eamondoherty618-prog/tracker-firmware/src/can_obd2.cpp

#include "can_obd2.h"

#include <Arduino.h>
#include "driver/twai.h"
#include "tracker_config.h"

// ISO 15765-4 CAN for OBD2: 11-bit functional request 0x7DF answered from
// 0x7E8-0x7EF, with a 29-bit fallback (0x18DB33F1 → 0x18DAF1xx) for vehicles
// that use extended addressing. Single-frame for live PIDs; ISO-TP multi-frame
// (first frame → flow control → consecutive frames) for VIN and long DTC lists.

namespace {

enum class BusState : uint8_t {
  UNINSTALLED,   // driver not installed (boot, or torn down after failed probe)
  LISTENING,     // passive (LISTEN_ONLY): confirm healthy 500k traffic first
  PROBING,       // sending detection requests, waiting for any ECU to answer
  READY,         // bus confirmed — normal polling
  ABSENT,        // probe failed — dormant until the next re-probe window
};

enum class Op : uint8_t { NONE, PROBE, PID, DTC_STORED, DTC_PENDING, VIN, CLEAR };

BusState g_state = BusState::UNINSTALLED;
bool g_extended = false;          // 29-bit addressing in use
uint8_t g_probeAttempts = 0;
uint32_t g_nextProbeMs = 0;       // when ABSENT: earliest re-probe
uint32_t g_lastPollMs = 0;
uint32_t g_lastDtcPollMs = 0;

// In-flight request
Op g_op = Op::NONE;
uint8_t g_opPid = 0;
uint32_t g_opDeadlineMs = 0;
uint8_t g_pidIndex = 0;           // which configured PID the poll cycle is on

// Live values (NAN/negative = never read); *_ms = when last updated
const uint8_t kPids[] = TRACKER_OBD_PIDS;
constexpr size_t kPidCount = sizeof(kPids) / sizeof(kPids[0]);
float g_pidValue[kPidCount];
uint32_t g_pidMs[kPidCount];

// DTCs (decoded "P0301" style), VIN, clear handshake
constexpr size_t MAX_DTC = 8;
String g_dtc[MAX_DTC];      size_t g_dtcCount = 0;
String g_dtcPending[MAX_DTC]; size_t g_dtcPendingCount = 0;
bool g_dtcEverRead = false;
// New-code detection for the instant-post path: a stored-DTC set that changed
// vs the previous read this boot shouldn't wait out the telemetry cadence.
String g_dtcSig; bool g_dtcSigValid = false;
bool g_newDtcEvent = false;
// DTC collection windows: responses from every ECU merge into staging until
// the op deadline, then swap into the live lists in one deterministic step.
String g_dtcStage[MAX_DTC];     size_t g_dtcStageCount = 0;     bool g_dtcWindowGot = false;
String g_dtcPendStage[MAX_DTC]; size_t g_dtcPendStageCount = 0; bool g_dtcPendWindowGot = false;
uint32_t g_lastRxMs = 0;        // last frame heard in READY — silence demotes
uint8_t g_vinTries = 0;         // VIN retry budget per boot
bool g_surveySkipOnce = false;  // heartbeat builder: drop survey when body > budget
// Cold-start crank-voltage capture
bool g_wasRunning = false;
bool g_crankCapture = false;
uint32_t g_crankCaptureEndMs = 0;
float g_crankVMin = NAN;         // min seen during the active capture window
float g_crankVReport = NAN;      // latched result awaiting one telemetry post
String g_vin;
uint32_t g_vinNextMs = 0;   // next VIN request time; retries until captured
bool g_clearRequested = false;
bool g_clearedFlag = false;       // reported once in the next full payload

// ISO-TP reassembly
struct IsoTp {
  bool active = false;
  uint32_t respId = 0;
  uint16_t expected = 0;
  uint16_t got = 0;
  uint8_t nextSn = 1;
  uint32_t lastMs = 0;
  uint8_t buf[64];
} g_isotp;

uint32_t functionalReqId() { return g_extended ? 0x18DB33F1UL : 0x7DFUL; }

bool isObdResponseId(uint32_t id, bool extd) {
  if (g_extended) return extd && (id & 0x1FFFFF00UL) == 0x18DAF100UL;
  return !extd && id >= 0x7E8 && id <= 0x7EF;
}

// Flow-control frame goes to the specific ECU that sent the first frame.
uint32_t flowControlId(uint32_t respId) {
  if (g_extended) {
    const uint8_t ecu = respId & 0xFF;             // 0x18DAF1<ecu>
    return 0x18DA0000UL | ((uint32_t)ecu << 8) | 0xF1UL;  // 0x18DA<ecu>F1
  }
  return respId - 8;                               // 0x7E8 → 0x7E0
}

bool sendFrame(uint32_t id, const uint8_t* data, uint8_t len) {
  twai_message_t msg = {};
  msg.identifier = id;
  msg.extd = g_extended ? 1 : 0;
  // Single-shot: NO hardware retransmission. On a sleeping bus an un-ACKed
  // frame parks the controller at error-passive (bus-off is unreachable) and
  // the TWAI peripheral retransmits it forever — jamming the vehicle's OBD
  // bus all night. Request/response already has op-level timeouts; a lost
  // request is simply retried by the next poll.
  msg.ss = 1;
  msg.data_length_code = 8;                        // ISO 15765-4: pad to 8
  memset(msg.data, 0x00, 8);
  memcpy(msg.data, data, len);
  const bool ok = twai_transmit(&msg, pdMS_TO_TICKS(20)) == ESP_OK;
#if TRACKER_BENCH_DEBUG
  Serial.printf("CAN TX %08lx:", (unsigned long)id);
  for (int i = 0; i < 8; i++) Serial.printf(" %02x", msg.data[i]);
  Serial.println(ok ? "" : "  (tx failed)");
#endif
  return ok;
}

bool sendRequest(const uint8_t* payload, uint8_t len) {
  uint8_t f[8] = { len };
  memcpy(f + 1, payload, len);
  return sendFrame(functionalReqId(), f, len + 1);
}

void beginOp(Op op, uint8_t pid, uint32_t timeoutMs) {
  g_op = op;
  g_opPid = pid;
  g_opDeadlineMs = millis() + timeoutMs;
  g_isotp.active = false;
}

bool startRequestForOp(Op op, uint8_t pid) {
  switch (op) {
    case Op::PROBE:
    case Op::PID: {
      const uint8_t r[] = { 0x01, pid };
      return sendRequest(r, 2);
    }
    case Op::DTC_STORED: { const uint8_t r[] = { 0x03 }; return sendRequest(r, 1); }
    case Op::DTC_PENDING: { const uint8_t r[] = { 0x07 }; return sendRequest(r, 1); }
    case Op::VIN: { const uint8_t r[] = { 0x09, 0x02 }; return sendRequest(r, 2); }
    case Op::CLEAR: { const uint8_t r[] = { 0x04 }; return sendRequest(r, 1); }
    default: return false;
  }
}

// Decode one DTC byte pair to the standard P/C/B/U code string.
String decodeDtc(uint8_t a, uint8_t b) {
  static const char kSys[4] = { 'P', 'C', 'B', 'U' };
  char code[6];
  snprintf(code, sizeof(code), "%c%01X%01X%01X%01X",
           kSys[(a >> 6) & 0x3], (a >> 4) & 0x3, a & 0xF, (b >> 4) & 0xF, b & 0xF);
  return String(code);
}

void parseDtcPayload(const uint8_t* d, uint16_t len, String* out, size_t* outCount) {
  // d[0] = 0x43/0x47, d[1] = count, then 2-byte pairs.
  *outCount = 0;
  if (len < 2) return;
  const uint8_t n = d[1];
  for (uint8_t i = 0; i < n && *outCount < MAX_DTC; i++) {
    const uint16_t off = 2 + i * 2;
    if (off + 1 >= len) break;
    if (d[off] == 0 && d[off + 1] == 0) continue;  // padding pair
    out[(*outCount)++] = decodeDtc(d[off], d[off + 1]);
  }
}

void handlePidValue(uint8_t pid, const uint8_t* ab, uint16_t len) {
  // Key-off placeholder filter: as the bus winds down the ECU answers with
  // 0xFF-filled data ("no value") for a moment. Decoded blindly that's
  // 255 km/h and 100% throttle frozen on the app's vitals card. All-FF is
  // never a legitimate reading for the PIDs we poll — drop the response.
  bool allFF = len > 0;
  for (uint16_t i = 0; i < len; i++) {
    if (ab[i] != 0xFF) { allFF = false; break; }
  }
  if (allFF) return;

  float v = NAN;
  switch (pid) {
    case 0x0C: if (len >= 2) v = ((ab[0] << 8) | ab[1]) / 4.0f; break;  // RPM
    case 0x0D: if (len >= 1) v = ab[0]; break;                          // km/h
    case 0x05: if (len >= 1) v = (float)ab[0] - 40.0f; break;           // coolant °C
    case 0x11: if (len >= 1) v = ab[0] * 100.0f / 255.0f; break;        // throttle %
    case 0x42: if (len >= 2) v = ((ab[0] << 8) | ab[1]) / 1000.0f; break; // control module voltage
    case 0x2F: if (len >= 1) v = ab[0] * 100.0f / 255.0f; break;        // fuel level %
    case 0x10: if (len >= 2) v = ((ab[0] << 8) | ab[1]) / 100.0f; break; // MAF grams/sec
    default:   if (len >= 1) v = ab[0]; break;   // raw first byte for extra PIDs
  }
  for (size_t i = 0; i < kPidCount; i++) {
    if (kPids[i] == pid && !isnan(v)) { g_pidValue[i] = v; g_pidMs[i] = millis(); }
  }

  // Cold-start forensics: capture the LOWEST control-module voltage (PID 0x42)
  // during the engine-start window — the crank/alternator-ramp sag. Trended
  // server-side over weeks, a deepening sag calls a dying battery BEFORE it
  // strands the truck. (True hardware note: this is the sag the tracker can
  // see once it's polling — the deepest starter-motor dip may pre-date the
  // first poll, but the trend of what we DO catch is what matters.)
  if (pid == 0x42 && g_crankCapture && !isnan(v) && v > 6.0f) {
    if (isnan(g_crankVMin) || v < g_crankVMin) g_crankVMin = v;
  }
}

// A fully reassembled (or single-frame) OBD payload for the in-flight op.
// Union one responder's codes into a staging set (dedup, capped). DTC ops
// collect from ALL ECUs until the op deadline — first-responder-wins made the
// visible set oscillate ECM/TCM and spam instant posts.
void mergeDtcPayload(const uint8_t* d, uint16_t len, String* out, size_t* outCount) {
  String tmp[MAX_DTC]; size_t n = 0;
  parseDtcPayload(d, len, tmp, &n);
  for (size_t i = 0; i < n && *outCount < MAX_DTC; i++) {
    bool dup = false;
    for (size_t j = 0; j < *outCount; j++) if (out[j] == tmp[i]) { dup = true; break; }
    if (!dup) out[(*outCount)++] = tmp[i];
  }
}

void handleObdPayload(const uint8_t* d, uint16_t len) {
  if (len < 1) return;
  const uint8_t svc = d[0];
  // Cross-ECU discipline: a broadcast (0x7DF) request is answered by EVERY
  // emissions ECU. Only a payload that MATCHES the in-flight op may consume
  // it — a TCM's 0x7F negative response must not cancel the ECM's multi-frame
  // VIN mid-reassembly (field bug: the truck's VIN could NEVER be captured
  // because unconditional g_op=NONE ran on the first stray reply). Unmatched
  // payloads are ignored; the op deadline handles true timeouts.
  bool done = false;
  switch (g_op) {
    case Op::PROBE:
      if (svc == 0x41) {
        g_state = BusState::READY;
        g_lastRxMs = millis();
        g_probeAttempts = 0;
        Serial.print("OBD2: bus detected (");
        Serial.print(g_extended ? "29" : "11");
        Serial.println("-bit)");
        if (len >= 4) handlePidValue(d[1], d + 2, len - 2);
        done = true;
      }
      break;
    case Op::PID:
      if (svc == 0x41 && len >= 3 && d[1] == g_opPid) { handlePidValue(d[1], d + 2, len - 2); done = true; }
      break;
    case Op::DTC_STORED:
      // Collect-until-deadline: merge into staging; finalize in canObd2Service.
      if (svc == 0x43) { mergeDtcPayload(d, len, g_dtcStage, &g_dtcStageCount); g_dtcWindowGot = true; }
      break;
    case Op::DTC_PENDING:
      if (svc == 0x47) { mergeDtcPayload(d, len, g_dtcPendStage, &g_dtcPendStageCount); g_dtcPendWindowGot = true; }
      break;
    case Op::VIN:
      // [0x49, 0x02, 0x01, 17 VIN chars]
      if (svc == 0x49 && len >= 4) {
        String vin;
        for (uint16_t i = 3; i < len && vin.length() < 17; i++) {
          const char c = (char)d[i];
          if (c >= '0' && c <= 'Z') vin += c;
        }
        if (vin.length() == 17) { g_vin = vin; Serial.print("OBD2: VIN "); Serial.println(g_vin); done = true; }
      }
      break;
    case Op::CLEAR:
      if (svc == 0x44) {
        g_dtcCount = 0;
        g_dtcPendingCount = 0;
        g_dtcSig = "";
        g_clearedFlag = true;
        Serial.println("OBD2: stored DTCs cleared (server-commanded)");
        done = true;
      }
      break;
    default: break;
  }
  if (done) g_op = Op::NONE;
}

void handleFrame(const twai_message_t& msg) {
#if TRACKER_BENCH_DEBUG
  Serial.printf("CAN RX %08lx:", (unsigned long)msg.identifier);
  for (int i = 0; i < msg.data_length_code; i++) Serial.printf(" %02x", msg.data[i]);
  Serial.println();
#endif
  if (!isObdResponseId(msg.identifier, msg.extd)) return;
  const uint8_t* d = msg.data;
  const uint8_t pci = d[0] >> 4;

  if (pci == 0x0) {                                   // single frame
    const uint8_t len = d[0] & 0xF;
    if (len >= 1 && len <= 7) handleObdPayload(d + 1, len);
  } else if (pci == 0x1) {                            // first frame → flow control
    // First FF wins: a second ECU's multi-frame answer must not clobber an
    // in-progress reassembly (cross-ECU broadcast responses).
    if (g_isotp.active && msg.identifier != g_isotp.respId) return;
    g_isotp.active = true;
    g_isotp.respId = msg.identifier;
    g_isotp.expected = ((d[0] & 0xF) << 8) | d[1];
    if (g_isotp.expected > sizeof(g_isotp.buf)) g_isotp.expected = sizeof(g_isotp.buf);
    g_isotp.got = 0;
    g_isotp.nextSn = 1;
    g_isotp.lastMs = millis();
    for (uint8_t i = 2; i < 8 && g_isotp.got < g_isotp.expected; i++) g_isotp.buf[g_isotp.got++] = d[i];
    const uint8_t fc[] = { 0x30, 0x00, 0x00 };        // continue, no block limit, no delay
    sendFrame(flowControlId(msg.identifier), fc, 3);
  } else if (pci == 0x2 && g_isotp.active && msg.identifier == g_isotp.respId) {  // consecutive
    if ((d[0] & 0xF) != (g_isotp.nextSn & 0xF)) { g_isotp.active = false; return; }
    g_isotp.nextSn++;
    g_isotp.lastMs = millis();
    for (uint8_t i = 1; i < 8 && g_isotp.got < g_isotp.expected; i++) g_isotp.buf[g_isotp.got++] = d[i];
    if (g_isotp.got >= g_isotp.expected) {
      g_isotp.active = false;
      handleObdPayload(g_isotp.buf, g_isotp.got);
    }
  }
}

bool installDriver(bool listenOnly) {
  // LISTEN_ONLY is physically passive: no TX, not even ACK bits. The probe
  // starts there so a mis-wired tap or wrong-bitrate bus can't be disturbed
  // by us — a live vehicle bus carries power steering and worse (field:
  // plugging an unpowered, terminated tap bumped the idle and latched a
  // "service power steering" warning).
  twai_general_config_t g = TWAI_GENERAL_CONFIG_DEFAULT(
      (gpio_num_t)TRACKER_CAN_TX_GPIO, (gpio_num_t)TRACKER_CAN_RX_GPIO,
      listenOnly ? TWAI_MODE_LISTEN_ONLY : TWAI_MODE_NORMAL);
  g.rx_queue_len = 32;
  g.tx_queue_len = 4;
  twai_timing_config_t t = TWAI_TIMING_CONFIG_500KBITS();
  twai_filter_config_t f = TWAI_FILTER_CONFIG_ACCEPT_ALL();
  if (twai_driver_install(&g, &t, &f) != ESP_OK) return false;
  if (twai_start() != ESP_OK) { twai_driver_uninstall(); return false; }
  return true;
}

void teardownDriver() {
  twai_stop();
  twai_driver_uninstall();
}

void goAbsent() {
  teardownDriver();
  g_state = BusState::ABSENT;
  g_nextProbeMs = millis() + TRACKER_OBD_REPROBE_MS;
  g_op = Op::NONE;
  Serial.println("OBD2: no bus detected — dormant (will re-probe when the vehicle is active)");
}

uint32_t g_listenStartMs = 0;
uint32_t g_listenFrames = 0;

// Passive bus survey: an inventory of every CAN ID heard with its latest
// payload bytes. This is the discovery tool for proprietary broadcasts the
// standard OBD2 services can't reach (e.g. GM TPMS tire pressures): deflate a
// tire, watch which ID's byte moves in telemetry. RX-only — gathering it
// never transmits a single frame.
struct SurveyEntry { uint32_t id; uint32_t count; uint8_t len; uint8_t data[8]; };
constexpr size_t MAX_SURVEY = 48;
SurveyEntry g_survey[MAX_SURVEY];
size_t g_surveyCount = 0;

void surveyFrame(const twai_message_t& msg) {
  for (size_t i = 0; i < g_surveyCount; i++) {
    if (g_survey[i].id == msg.identifier) {
      g_survey[i].count++;
      g_survey[i].len = msg.data_length_code;
      memcpy(g_survey[i].data, msg.data, 8);
      return;
    }
  }
  if (g_surveyCount < MAX_SURVEY) {
    SurveyEntry& e = g_survey[g_surveyCount++];
    e.id = msg.identifier;
    e.count = 1;
    e.len = msg.data_length_code;
    memcpy(e.data, msg.data, 8);
  }
}

void startProbe() {
  // Phase 1: passive listen. Healthy 500k traffic (frames received, no bus
  // errors) is required before we ever transmit a bit.
  if (g_state == BusState::UNINSTALLED || g_state == BusState::ABSENT) {
    if (!installDriver(true)) { g_state = BusState::ABSENT; g_nextProbeMs = millis() + TRACKER_OBD_REPROBE_MS; return; }
  }
  g_state = BusState::LISTENING;
  g_listenStartMs = millis();
  g_listenFrames = 0;
  g_probeAttempts = 0;
  g_extended = false;
  g_op = Op::NONE;
}

}  // namespace

void canObd2Init() {
  for (size_t i = 0; i < kPidCount; i++) { g_pidValue[i] = NAN; g_pidMs[i] = 0; }

#if TRACKER_BENCH_DEBUG
  // RX idle check: a powered, healthy transceiver holds RXD HIGH (recessive)
  // when the bus is quiet. LOW/floating here = dead unit logic or a broken
  // white lead — distinguishes them from ESP32-side faults without a meter.
  pinMode(TRACKER_CAN_RX_GPIO, INPUT);
  delay(5);
  Serial.printf("CAN: RX line idle = %s (HIGH = transceiver alive)\n",
                digitalRead(TRACKER_CAN_RX_GPIO) ? "HIGH" : "LOW");
#endif

#if TRACKER_BENCH_DEBUG && !TRACKER_CAN_LISTEN_ONLY_LOCK
  // Line-load test: drive TX as a plain GPIO and read it back. A healthy,
  // unpowered-or-listening transceiver input barely loads the pin; a damaged
  // TXD input clamps it, and the readback disagrees with what we drive.
  {
    pinMode(TRACKER_CAN_TX_GPIO, OUTPUT);
    digitalWrite(TRACKER_CAN_TX_GPIO, HIGH);
    delayMicroseconds(50);
    const int readHigh = digitalRead(TRACKER_CAN_TX_GPIO);
    digitalWrite(TRACKER_CAN_TX_GPIO, LOW);
    delayMicroseconds(50);
    const int readLow = digitalRead(TRACKER_CAN_TX_GPIO);
    digitalWrite(TRACKER_CAN_TX_GPIO, HIGH);  // leave recessive
    Serial.printf("CAN: TX line-load test: drive HIGH reads %s, drive LOW reads %s%s\n",
                  readHigh ? "HIGH" : "LOW", readLow ? "LOW(ok)" : "LOW(ok)",
                  readHigh ? " — line free" : " — LINE CLAMPED (unit TXD input suspect)");
    pinMode(TRACKER_CAN_TX_GPIO, INPUT);
  }

  // Desk self-test: transmit one frame in NO_ACK mode and listen for our own
  // echo through the transceiver. Straight TX/RX wiring = echo received;
  // crossed Grove leads = silence. This resolves the wiring question WITHOUT
  // a vehicle (bench only — this mode transmits, so it is compiled out of
  // bench_listen and must never run plugged into a live bus).
  {
    twai_general_config_t g = TWAI_GENERAL_CONFIG_DEFAULT(
        (gpio_num_t)TRACKER_CAN_TX_GPIO, (gpio_num_t)TRACKER_CAN_RX_GPIO, TWAI_MODE_NO_ACK);
    twai_timing_config_t t = TWAI_TIMING_CONFIG_500KBITS();
    twai_filter_config_t f = TWAI_FILTER_CONFIG_ACCEPT_ALL();
    bool pass = false;
    if (twai_driver_install(&g, &t, &f) == ESP_OK && twai_start() == ESP_OK) {
      twai_message_t tx = {};
      tx.identifier = 0x555;
      tx.self = 1;               // self-reception request: loop back via the bus pins
      tx.data_length_code = 2;
      tx.data[0] = 0xAB; tx.data[1] = 0xCD;
      if (twai_transmit(&tx, pdMS_TO_TICKS(100)) == ESP_OK) {
        twai_message_t rx;
        if (twai_receive(&rx, pdMS_TO_TICKS(300)) == ESP_OK && rx.identifier == 0x555) pass = true;
      }
      // Error autopsy: the counters say WHY an echo died. High bus/tx errors =
      // we transmitted but the bus never reflected it (transceiver mute or
      // dead driver). Clean counters + no echo = frame never made it out.
      twai_status_info_t st;
      if (twai_get_status_info(&st) == ESP_OK) {
        Serial.printf("CAN: post-test state=%d tx_err=%lu rx_err=%lu bus_err=%lu tx_failed=%lu arb_lost=%lu\n",
                      (int)st.state, (unsigned long)st.tx_error_counter, (unsigned long)st.rx_error_counter,
                      (unsigned long)st.bus_error_count, (unsigned long)st.tx_failed_count,
                      (unsigned long)st.arb_lost_count);
      }
      twai_stop();
      twai_driver_uninstall();
    }
    Serial.println(pass
      ? "CAN self-test: PASS — TX/RX wiring to the transceiver is good"
      : "CAN self-test: FAIL — no echo; yellow/white Grove leads likely crossed (or unit unpowered)");

    // Slow-speed retry: marginal/damaged analog paths sometimes pass at
    // 125 kbps while failing at 500. A split verdict is its own fingerprint.
    if (!pass) {
      twai_general_config_t g2 = TWAI_GENERAL_CONFIG_DEFAULT(
          (gpio_num_t)TRACKER_CAN_TX_GPIO, (gpio_num_t)TRACKER_CAN_RX_GPIO, TWAI_MODE_NO_ACK);
      twai_timing_config_t t2 = TWAI_TIMING_CONFIG_125KBITS();
      twai_filter_config_t f2 = TWAI_FILTER_CONFIG_ACCEPT_ALL();
      bool slowPass = false;
      if (twai_driver_install(&g2, &t2, &f2) == ESP_OK && twai_start() == ESP_OK) {
        twai_message_t tx2 = {};
        tx2.identifier = 0x556;
        tx2.self = 1;
        tx2.data_length_code = 1;
        tx2.data[0] = 0x5A;
        if (twai_transmit(&tx2, pdMS_TO_TICKS(100)) == ESP_OK) {
          twai_message_t rx2;
          if (twai_receive(&rx2, pdMS_TO_TICKS(300)) == ESP_OK && rx2.identifier == 0x556) slowPass = true;
        }
        twai_stop();
        twai_driver_uninstall();
      }
      Serial.println(slowPass
        ? "CAN self-test @125k: PASS — analog path marginal at 500k (damaged but limping)"
        : "CAN self-test @125k: FAIL — transmit path hard-dead at any speed");
    }
  }
#endif

  startProbe();
}

void canObd2RequestClearDtc() {
  if (g_state != BusState::READY) { Serial.println("OBD2: clear requested but bus not present"); return; }
  g_clearRequested = true;
}

bool canObd2Present() { return g_state == BusState::READY; }

bool canObd2TakeNewDtcEvent() {
  const bool e = g_newDtcEvent;
  g_newDtcEvent = false;
  return e;
}

bool canObd2EngineRunning() {
  // Fresh RPM (0x0C) reading above the idle floor = engine on.
  for (size_t i = 0; i < kPidCount; i++) {
    if (kPids[i] == 0x0C) {
      return g_pidMs[i] != 0 && (millis() - g_pidMs[i] < 15000UL) && g_pidValue[i] > 250.0f;
    }
  }
  return false;
}

void canObd2Service(bool vehicleActive) {
  const uint32_t now = millis();

  // Drain everything the controller has for us — cheap, no blocking.
  if (g_state == BusState::PROBING || g_state == BusState::READY) {
    twai_message_t msg;
    while (twai_receive(&msg, 0) == ESP_OK) { g_lastRxMs = now; surveyFrame(msg); handleFrame(msg); }

    // A wedged controller (no transceiver → no ACKs → bus-off) reads as absent.
    twai_status_info_t st;
    if (twai_get_status_info(&st) == ESP_OK && st.state == TWAI_STATE_BUS_OFF) {
      goAbsent();
      return;
    }
  }

  // ISO-TP reassembly timeout
  if (g_isotp.active && now - g_isotp.lastMs > 500) g_isotp.active = false;

  switch (g_state) {
    case BusState::ABSENT:
      // Re-probe on a timer regardless of trip state (the listen phase is
      // passive and harmless on a sleeping bus). Field lesson: an unlucky
      // boot window marked the bus absent and, gated on GPS-motion trips,
      // never retried while the truck idled in the driveway for an hour.
      if ((int32_t)(now - g_nextProbeMs) >= 0) startProbe();
      return;
    case BusState::UNINSTALLED:
      return;
    case BusState::LISTENING: {
#if TRACKER_BENCH_DEBUG
      // Silence must be visible: prove the listener is alive even when the
      // bus is dead quiet (parked truck, desk bench, unplugged tap).
      static uint32_t lastListenLogMs = 0;
      if (now - lastListenLogMs >= 10000UL) {
        lastListenLogMs = now;
        Serial.printf("CAN: listening (%s), %lu frames heard\n",
                      TRACKER_CAN_LISTEN_ONLY_LOCK ? "locked passive" : "pre-probe",
                      (unsigned long)g_listenFrames);
      }
#endif
      // Count anything heard; healthy traffic ⇒ safe to speak. Silence for
      // the whole window ⇒ treat as absent (or parked) and stay passive.
      twai_message_t msg;
      while (twai_receive(&msg, 0) == ESP_OK) {
        g_listenFrames++;
        surveyFrame(msg);
#if TRACKER_BENCH_DEBUG
        if (g_listenFrames <= 5) {
          Serial.printf("CAN LISTEN %08lx dlc=%d\n", (unsigned long)msg.identifier, msg.data_length_code);
        }
#endif
      }
      if (TRACKER_CAN_LISTEN_ONLY_LOCK) {
        // Locked passive: report what we hear, never speak. Frame count goes
        // out in telemetry so the first vehicle session is verifiable without
        // a laptop.
        return;
      }
      // Threshold/window tuned on a live 2017 Silverado: the main loop blocks
      // for seconds at a time during boot (modem bring-up), so early drains
      // only catch a queue's worth of frames — 5s was expiring before 20
      // frames ever accumulated even on a roaring bus. 5 real frames is
      // already unambiguous; give the window 30s to survive boot congestion.
      if (g_listenFrames >= 5) {
        // Real traffic at 500k confirmed — switch to normal mode and probe.
        teardownDriver();
        if (!installDriver(false)) { g_state = BusState::ABSENT; g_nextProbeMs = now + TRACKER_OBD_REPROBE_MS; return; }
        Serial.println("OBD2: bus traffic heard — probing");
        g_state = BusState::PROBING;
        g_probeAttempts = 0;
        g_extended = false;
      } else if (now - g_listenStartMs > 30000) {
        goAbsent();
      }
      return;
    }
    case BusState::PROBING: {
      if (g_op == Op::PROBE && (int32_t)(now - g_opDeadlineMs) < 0) return;  // await answer
      if (g_op == Op::PROBE) {                       // timed out
        g_op = Op::NONE;
        g_probeAttempts++;
        if (g_probeAttempts >= 3) {
          if (!g_extended) { g_extended = true; g_probeAttempts = 0; }  // try 29-bit
          else { goAbsent(); return; }
        }
      }
      beginOp(Op::PROBE, kPids[0], 400);
      startRequestForOp(Op::PROBE, kPids[0]);
      return;
    }
    case BusState::READY:
      break;
  }

  // Bus silent 60s in READY (engine off → ECUs asleep): stand down to the
  // passive re-probe instead of transmitting at a dead bus. (With ss=1 frames
  // aren't hardware-retried, but polling a sleeping bus is still pointless
  // chatter and delays detecting the next engine start cleanly.)
  if (g_lastRxMs != 0 && now - g_lastRxMs > 60000UL) {
    Serial.println("OBD2: bus silent 60s — standing down to passive re-probe");
    twai_clear_transmit_queue();
    teardownDriver();
    g_state = BusState::ABSENT;
    g_lastRxMs = 0;
    g_nextProbeMs = now + TRACKER_OBD_REPROBE_MS;
    return;
  }

  // READY: one in-flight request at a time, next step chosen by priority.
  if (g_op != Op::NONE) {
    if ((int32_t)(now - g_opDeadlineMs) < 0) return;   // still waiting
    // Op window closed. DTC ops COLLECT until this deadline (multi-ECU
    // union) and finalize here in one deterministic step.
    if (g_op == Op::DTC_STORED && g_dtcWindowGot) {
      for (size_t i = 0; i < g_dtcStageCount; i++) g_dtc[i] = g_dtcStage[i];
      g_dtcCount = g_dtcStageCount;
      g_dtcEverRead = true;
      String sig;
      for (size_t i = 0; i < g_dtcCount; i++) { sig += g_dtc[i]; sig += ','; }
      // First read of the boot only baselines; codes already present ride the
      // next normal post. A set that changes mid-session fires instantly.
      if (g_dtcSigValid && sig != g_dtcSig && g_dtcCount > 0) g_newDtcEvent = true;
      g_dtcSig = sig;
      g_dtcSigValid = true;
    } else if (g_op == Op::DTC_PENDING && g_dtcPendWindowGot) {
      for (size_t i = 0; i < g_dtcPendStageCount; i++) g_dtcPending[i] = g_dtcPendStage[i];
      g_dtcPendingCount = g_dtcPendStageCount;
    }
    g_op = Op::NONE;
  }

  if (g_clearRequested) {
    g_clearRequested = false;
    beginOp(Op::CLEAR, 0, 800);
    startRequestForOp(Op::CLEAR, 0);
    return;
  }
  // VIN: retry until actually captured — the old one-shot fired once per boot
  // and lost its chance whenever the bus wasn't ready at that moment (field
  // bug: truck ran for days with no VIN bound). Re-ask every 2 min until the
  // 17 chars land; after that, never again this boot.
  if (g_vin.length() != 17 && g_vinTries < 10 &&
      (g_vinNextMs == 0 || (int32_t)(now - g_vinNextMs) >= 0)) {
    g_vinTries++;   // bounded per boot — a truck that won't answer isn't asked forever
    g_vinNextMs = now + 2 * 60 * 1000UL;
    beginOp(Op::VIN, 0, 800);
    startRequestForOp(Op::VIN, 0);
    return;
  }
  if (vehicleActive && now - g_lastDtcPollMs >= TRACKER_OBD_DTC_POLL_MS) {
    // Alternate stored/pending each window to keep bus chatter minimal.
    static bool pendingTurn = false;
    g_lastDtcPollMs = now;
    const Op op = pendingTurn ? Op::DTC_PENDING : Op::DTC_STORED;
    pendingTurn = !pendingTurn;
    // fresh collection window — every responder unions in until the deadline
    if (op == Op::DTC_STORED) { g_dtcStageCount = 0; g_dtcWindowGot = false; }
    else { g_dtcPendStageCount = 0; g_dtcPendWindowGot = false; }
    beginOp(op, 0, 800);
    startRequestForOp(op, 0);
    return;
  }
  // Cold-start capture: the instant the engine transitions to running (rpm
  // crosses the idle floor for the first time this bus session), open a 5s
  // window that polls ONLY voltage (0x42) fast, so handlePidValue can record
  // the crank/ramp sag minimum. One capture per engine start.
  const bool running = canObd2EngineRunning();
  if (running && !g_wasRunning) {
    g_crankCapture = true;
    g_crankCaptureEndMs = now + 5000UL;
    g_crankVMin = NAN;
  }
  g_wasRunning = running;
  if (g_crankCapture) {
    if ((int32_t)(now - g_crankCaptureEndMs) >= 0) {
      g_crankCapture = false;
      if (!isnan(g_crankVMin)) g_crankVReport = g_crankVMin;  // latch for one post
    } else if (g_op == Op::NONE && now - g_lastPollMs >= 120UL) {
      g_lastPollMs = now;
      beginOp(Op::PID, 0x42, 200);
      startRequestForOp(Op::PID, 0x42);
      return;
    }
  }

  // PIDs poll on every READY bus, not just on trips: parked-with-engine-on is
  // exactly the idling state the fleet features bill by, and trip detection is
  // GPS-motion-based so it can never see it. Parked polls run at a relaxed
  // cadence to keep bus chatter and data cost down.
  const uint32_t pollGap = vehicleActive ? (TRACKER_OBD_POLL_MS / kPidCount)
                                         : TRACKER_OBD_PARKED_POLL_MS;
  if (now - g_lastPollMs >= pollGap) {
    g_lastPollMs = now;
    const uint8_t pid = kPids[g_pidIndex];
    g_pidIndex = (g_pidIndex + 1) % kPidCount;
    beginOp(Op::PID, pid, 300);
    startRequestForOp(Op::PID, pid);
  }
}

// Consume-once: the crank-sag minimum voltage from the last engine start, or
// NAN if none captured since the last read. Rides one telemetry post.
float canObd2TakeCrankVMin() {
  const float v = g_crankVReport;
  g_crankVReport = NAN;
  return v;
}

void canObd2AppendTelemetry(JsonDocument& doc, bool compact) {
  const uint32_t now = millis();
  const bool present = canObd2Present();

  if (compact) {
    if (!present) return;                              // UDP budget: omit entirely
    JsonObject obd = doc["obd"].to<JsonObject>();
    for (size_t i = 0; i < kPidCount; i++) {
      if (g_pidMs[i] == 0 || now - g_pidMs[i] > 30000UL) continue;  // stale
      switch (kPids[i]) {
        case 0x0C: obd["rpm"] = (int)g_pidValue[i]; break;
        case 0x0D: obd["speed_kph"] = (int)g_pidValue[i]; break;
        case 0x05: obd["coolant_c"] = (int)g_pidValue[i]; break;
        case 0x11: obd["throttle_pct"] = (int)g_pidValue[i]; break;
        // Voltage + fuel ride the compact/UDP payload too: they drive the
        // battery-health, low-fuel, and fuel-theft alerts, which must fire
        // without waiting for a full HTTPS heartbeat.
        case 0x42: obd["volt"] = serialized(String(g_pidValue[i], 1)); break;
        case 0x2F: obd["fuel_pct"] = (int)g_pidValue[i]; break;
        default: break;
      }
    }
    if (g_dtcEverRead) obd["dtc_count"] = (int)g_dtcCount;
    return;
  }

  JsonObject obd = doc["obd"].to<JsonObject>();
  obd["present"] = present;
  if (g_state == BusState::LISTENING && g_listenFrames > 0) {
    obd["listen_frames"] = g_listenFrames;  // passive session: bus heard, not spoken to
  }

  // Bus survey: rotating window of 6 entries per post ("id:count:hexbytes"),
  // sweeping the whole table across consecutive posts. SIZE MATTERS: the
  // modem's SHBOD body cap is 1024 B and the 10-entry window pushed full
  // payloads past it — every heartbeat died for a day (the 0.11.7 crash-loop
  // incident). 6 entries ≈ 180 B; the heartbeat builder also drops the whole
  // section (suppress-once) if the body still lands over budget.
  if (g_surveyCount > 0 && !g_surveySkipOnce) {
    JsonArray sv = obd["can_ids"].to<JsonArray>();
    static size_t cursor = 0;
    const size_t n = g_surveyCount < 6 ? g_surveyCount : 6;
    for (size_t k = 0; k < n; k++) {
      const SurveyEntry& e = g_survey[(cursor + k) % g_surveyCount];
      char hex[17];
      const uint8_t hb = e.len > 8 ? 8 : e.len;
      for (uint8_t b = 0; b < hb; b++) sprintf(hex + b * 2, "%02X", e.data[b]);
      hex[hb * 2] = '\0';
      char buf[40];
      snprintf(buf, sizeof(buf), "%lX:%lu:%s", (unsigned long)e.id, (unsigned long)e.count, hex);
      sv.add(String(buf));
    }
    cursor = (cursor + n) % g_surveyCount;
    obd["can_ids_total"] = (int)g_surveyCount;
  }

  if (!present) return;
  obd["addr"] = g_extended ? "29bit" : "11bit";
  for (size_t i = 0; i < kPidCount; i++) {
    if (g_pidMs[i] == 0 || now - g_pidMs[i] > 30000UL) continue;
    switch (kPids[i]) {
      case 0x0C: obd["rpm"] = (int)g_pidValue[i]; break;
      case 0x0D: obd["speed_kph"] = (int)g_pidValue[i]; break;
      case 0x05: obd["coolant_c"] = (int)g_pidValue[i]; break;
      case 0x11: obd["throttle_pct"] = (int)g_pidValue[i]; break;
      case 0x42: obd["volt"] = serialized(String(g_pidValue[i], 2)); break;      // control module V
      case 0x2F: obd["fuel_pct"] = (int)g_pidValue[i]; break;                    // fuel level %
      case 0x10: obd["maf_gps"] = serialized(String(g_pidValue[i], 1)); break;   // for MPG calc
      default: { char k[8]; snprintf(k, sizeof(k), "pid_%02x", kPids[i]); obd[k] = g_pidValue[i]; }
    }
  }
  if (g_vin.length() == 17) obd["vin"] = g_vin;
  if (g_dtcEverRead) {
    JsonArray dtc = obd["dtc"].to<JsonArray>();
    for (size_t i = 0; i < g_dtcCount; i++) dtc.add(g_dtc[i]);
    JsonArray pend = obd["dtc_pending"].to<JsonArray>();
    for (size_t i = 0; i < g_dtcPendingCount; i++) pend.add(g_dtcPending[i]);
  }
  if (g_clearedFlag) { obd["dtc_cleared"] = true; g_clearedFlag = false; }
  g_surveySkipOnce = false;   // one full build only
}

void canObd2SuppressSurveyOnce() { g_surveySkipOnce = true; }
